nsec/nsec-badge/hw/2025/sao/Sao_Diamond/jlcpcb/production_files/BOM-Sao_Diamond.csv

Comment | Designator | Footprint | LCSC | Quantity
LED | D2 | LED_D3.0mm |  | 1
LED | D1 | LED_D3.0mm |  | 1
330 | R1 | R_Axial_DIN0204_L3.6mm_D1.6mm_P7.62mm_Horizontal |  | 1
330 | R2 | R_Axial_DIN0204_L3.6mm_D1.6mm_P7.62mm_Horizontal |  | 1
SAO Connector SMD | J1 | SAO Connector SMD |  | 1
