nsec/nsec-badge/hw/2025/sao/Sao_SlotMachine_v2/jlcpcb/production_files/BOM-Sao_SlotMachine_v2.csv

Comment | Designator | Footprint | LCSC | Quantity
330 | R3 | R_0805_2012Metric_Pad1.20x1.40mm_HandSolder |  | 1
330 | R1 | R_0805_2012Metric_Pad1.20x1.40mm_HandSolder |  | 1
330 | R2 | R_0805_2012Metric_Pad1.20x1.40mm_HandSolder |  | 1
SAO Connector SMD | J1 | SAO Connector SMD |  | 1
LED | D2 | LED_1206_3216Metric_Pad1.42x1.75mm_HandSolder |  | 1
LED | D3 | LED_1206_3216Metric_Pad1.42x1.75mm_HandSolder |  | 1
LED | D1 | LED_1206_3216Metric_Pad1.42x1.75mm_HandSolder |  | 1
