nsec/nsec-badge/hw/2023/confBadge/gerber/2022-11-17_confBadgeV1b/CAMOutputs/Assembly/BOM_JLCSMT.xlsx

Comment | Designator | Footprint | JLCPCB Part #（optional）
0.1uF | C1 C2 C3 C4 C5 C6 C7 C8 C9 C10 C11 C12 C13 C14 C15 C16 C17 C18 C19 C20 | 0603-CAP | C14663
100K | R7 | 0603-NO | C25803
10118192-0002LF | J1 | AMPHENOL_10118192-0002LF | C132564
10K | R2 | 0603-RES | C25804
10uF | C27 | 0805-NO | C440198
1K | R13 R14 | 0603-NO | C21190
1uF | C21 C26 | 0603-NO | C15849
330r | R6 | 0603-RES | C23138
8/16/20MHz | Q1 | RESONATOR-SMD-1:1 | C32180
AP2112-3.3 | U2 | SOT23-5 | C150742
ATMEGA328 | U1 | TQFP32-08 | C14877
CH340C | U7 | SOIC127P600X180-16N | C84681
BTN | S2 S3 S5 S6 S7 S4 | TACTILE_SWITCH_SMD_5.2MM | C318884
MBR120 | D3 D4 | SOD-123 | C130880
RED | D1 D2 D5 | CHIPLED_0805_NOOUTLINE | C84256
SMF05CT1G | U8 | SOT65P210X110-6N | C558443
WS2812-2020 | U3 U4 U9 U10 U11 U12 U13 U14 U15 U16 U17 U18 U19 U20 U21 U22 | LED_WS2812-2020 | C965555
