nsec/nsec-badge/esp32/components/cmd/cmd.c

/* Console example

   This example code is in the Public Domain (or CC0 licensed, at your option.)

   Unless required by applicable law or agreed to in writing, this
   software is distributed on an "AS IS" BASIS, WITHOUT WARRANTIES OR
   CONDITIONS OF ANY KIND, either express or implied.
*/

#include "argtable3/argtable3.h"
#include "cmd_decl.h"
#include "driver/uart.h"
#include "esp_console.h"
#include "esp_log.h"
#include "esp_system.h"
#include "esp_vfs_dev.h"
#include "esp_vfs_fat.h"
#include "linenoise/linenoise.h"
#include "nvs.h"
#include "nvs_flash.h"
#include <stdio.h>
#include <string.h>

#include "cmd.h"

static const char *TAG = "console";

static struct {
    const char *n_line, *sec_line;
} nsec_rows[] = {
    // clang-format off
    {"                       ", "                                        `/ydmmmdy+.      "},
    {"                       ", "                                       /mNNmhyhmNNNy`    "},
    {"                       ", "                                      :NNN+`    -dNNh    "},
    {"     -ohy  `:+oo+/.    ", "  -+yhdmmdhyo/.      .:/+++/:.        /NNd-:/+++/oNNN`   "},
    {"  :hNMMMh-hMMMMMMMMNo  ", ":dNNNNNNNNNNNNNd. -sdNNNNNNNNNds-     /NNNNNNNNNNNNNm-   "},
    {"  sMMMMMNMMMMMMMMMMMMd ", "hNNNNmyssydNNNm/.yNNNNNNNNNNNNNNNy` `sNNNNNNNNNNNNNNNm/  "},
    {"  sMMMMMMMy+/+yNMMMMMM+", " NNNN/     `:o:-mNNNNmo-` `-sNNNNNd:mNNNNNdo:--:+yNms`   "},
    {"  sMMMMMN.     .NMMMMMy", " mNNNNho/-`   `mNNNNm-       /NNNNNNNNNNNo        ..     "},
    {"  sMMMMMh       hMMMMMy", " mNNNNNNNNNds/+NNNNNdsssssssssNNNNNNNNNNh                "},
    {"  sMMMMMh       hMMMMMy", " -odNNNNNNNNNNNNNNNNNNNNNNNNNNNNNNNNNNNNy                "},
    {"  sMMMMMh       hMMMMMy", "    `-/oydNNNNNNNNNNm:::::::::::::/NNNNNm.               "},
    {"  sMMMMMh       hMMMMMy", " o:`      .mNNNNNNNNNy.       -o-  sNNNNNm+`     .oy:    "},
    {"  sMMMMMh       hMMMMMy", " mNmhs+//+yNNNNNdNNNNNNhsoosymNNNh: omNNNNNNdhyhmNNNNh:  "},
    {"  sMMMMMh       hMMMMMy", " mNNNNNNNNNNNNNy`-ymNNNNNNNNNNNNmy-  .smNNNNNNNNNNNNms.  "},
    {"  +hhhhho       ohhhhho", " /shmNNNNNNmho-    `:oyhdmmmdyo:`      `:oyhdmmddyo:`    "},
    {"                       ", "      `..``                                              "},
    // clang-format on
};

void initialize_nvs(void)
{
    esp_err_t err = nvs_flash_init();
    if (err == ESP_ERR_NVS_NO_FREE_PAGES ||
        err == ESP_ERR_NVS_NEW_VERSION_FOUND) {
        ESP_ERROR_CHECK(nvs_flash_erase());
        err = nvs_flash_init();
    }
    ESP_ERROR_CHECK(err);
}

static void initialize_console(void)
{
    /* Drain stdout before reconfiguring it */
    fflush(stdout);
    fsync(fileno(stdout));

    /* Disable buffering on stdin */
    setvbuf(stdin, NULL, _IONBF, 0);

    /* Minicom, screen, idf_monitor send CR when ENTER key is pressed */
    esp_vfs_dev_uart_set_rx_line_endings(ESP_LINE_ENDINGS_CR);
    /* Move the caret to the beginning of the next line on '\n' */
    esp_vfs_dev_uart_set_tx_line_endings(ESP_LINE_ENDINGS_CRLF);

    /* Configure UART. Note that REF_TICK is used so that the baud rate remains
     * correct while APB frequency is changing in light sleep mode.
     */
    const uart_config_t uart_config = {
        .baud_rate = CONFIG_ESP_CONSOLE_UART_BAUDRATE,
        .data_bits = UART_DATA_8_BITS,
        .parity = UART_PARITY_DISABLE,
        .stop_bits = UART_STOP_BITS_1,
        .source_clk = UART_SCLK_REF_TICK,
    };
    /* Install UART driver for interrupt-driven reads and writes */
    ESP_ERROR_CHECK(
        uart_driver_install(CONFIG_ESP_CONSOLE_UART_NUM, 256, 0, 0, NULL, 0));
    ESP_ERROR_CHECK(
        uart_param_config(CONFIG_ESP_CONSOLE_UART_NUM, &uart_config));

    /* Tell VFS to use UART driver */
    esp_vfs_dev_uart_use_driver(CONFIG_ESP_CONSOLE_UART_NUM);

    /* Initialize the console */
    esp_console_config_t console_config = {
        .max_cmdline_args = 8,
        .max_cmdline_length = 256,
#if CONFIG_LOG_COLORS
        .hint_color = atoi(LOG_COLOR_CYAN)
#endif
    };
    ESP_ERROR_CHECK(esp_console_init(&console_config));

    /* Configure linenoise line completion library */
    /* Enable multiline editing. If not set, long commands will scroll within
     * single line.
     */
    linenoiseSetMultiLine(1);

    /* Tell linenoise where to get command completions and hints */
    linenoiseSetCompletionCallback(&esp_console_get_completion);
    linenoiseSetHintsCallback((linenoiseHintsCallback *)&esp_console_get_hint);

    /* Set command history size */
    linenoiseHistorySetMaxLen(100);
}

void console_task(void *parm)
{

    initialize_console();

    /* Diplay Nsec banner */
    fputc('\n', stdout);
    for (int i = 0; i < sizeof(nsec_rows) / sizeof(nsec_rows[0]); i++) {
        fwrite(nsec_rows[i].n_line, 1, strlen(nsec_rows[i].n_line), stdout);
        fwrite(nsec_rows[i].sec_line, 1, strlen(nsec_rows[i].sec_line), stdout);
        fputc('\n', stdout);
    }

    /* Register commands */
    esp_console_register_help_command();
    register_system();
    register_wifi();
    register_neopixel();

    // register_nvs();

    /* Prompt to be printed before each line.
     * This can be customized, made dynamic, etc.
     */
    const char *prompt = LOG_COLOR_I "nsec-badge> " LOG_RESET_COLOR;

    printf("\n"
           "Welcome to the nsec badge console!\n"
           "Type 'help' to get the list of commands.\n"
           "Use UP/DOWN arrows to navigate through command history.\n"
           "Press TAB when typing command name to auto-complete.\n");

    /* Figure out if the terminal supports escape sequences */
    int probe_status = linenoiseProbe();
    if (probe_status) { /* zero indicates success */
        printf("\n"
               "Your terminal application does not support escape sequences.\n"
               "Line editing and history features are disabled.\n"
               "On Windows, try using Putty instead.\n");
        linenoiseSetDumbMode(1);
#if CONFIG_LOG_COLORS
        /* Since the terminal doesn't support escape sequences,
         * don't use color codes in the prompt.
         */
        prompt = "nsec-badge> ";
#endif // CONFIG_LOG_COLORS
    }

    /* Main loop */
    while (true) {
        /* Get a line using linenoise.
         * The line is returned when ENTER is pressed.
         */
        char *line = linenoise(prompt);
        if (line == NULL) { /* Ignore empty lines */
            continue;
        }
        /* Add the command to the history */
        linenoiseHistoryAdd(line);

        /* Try to run the command */
        int ret;
        esp_err_t err = esp_console_run(line, &ret);
        if (err == ESP_ERR_NOT_FOUND) {
            printf("Unrecognized command\n");
        } else if (err == ESP_ERR_INVALID_ARG) {
            // command was empty
        } else if (err == ESP_OK && ret != ESP_OK) {
            printf("Command returned non-zero error code: 0x%x (%s)\n", ret,
                   esp_err_to_name(ret));
        } else if (err != ESP_OK) {
            printf("Internal error: %s\n", esp_err_to_name(err));
        }
        /* linenoise allocates line buffer on the heap, so need to free it */
        linenoiseFree(line);
    }
}
