nsec/nsec-badge/nrf52/nsec_led_settings.c

/*
 * Copyright 2018 Eric Tremblay <habscup@gmail.com>
 *
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
 * THE SOFTWARE IS PROVIDED "AS IS", WITHOUT WARRANTY OF ANY KIND, EXPRESS OR
 * IMPLIED, INCLUDING BUT NOT LIMITED TO THE WARRANTIES OF MERCHANTABILITY,
 * FITNESS FOR A PARTICULAR PURPOSE AND NONINFRINGEMENT. IN NO EVENT SHALL THE
 * AUTHORS OR COPYRIGHT HOLDERS BE LIABLE FOR ANY CLAIM, DAMAGES OR OTHER
 * LIABILITY, WHETHER IN AN ACTION OF CONTRACT, TORT OR OTHERWISE, ARISING FROM,
 * OUT OF OR IN CONNECTION WITH THE SOFTWARE OR THE USE OR OTHER DEALINGS IN THE
 * SOFTWARE.
 */

#include <nrf.h>
#include <nordic_common.h>
#include <stdio.h>
#include <stdbool.h>
#include "ble/nsec_ble.h"
#include "status_bar.h"
#include "app_glue.h"
#include "controls.h"
#include "nsec_led_settings.h"
#include "nsec_settings.h"
#include "menu.h"
#include "gfx_effect.h"
#include "ssd1306.h"
#include "ws2812fx.h"
#include "nsec_storage.h"

#define BRIGHNESS_MENU_INDEX        0

#define SUPER_LOW_BRIGHTNESS_INDEX  0
#define LOW_BRIGHTNESS_INDEX        1
#define MEDIUM_BRIGHTNESS_INDEX     2
#define HIGH_BRIGHTNESS_INDEX       3
#define MAX_BRIGHTNESS_INDEX        4

#define SUPER_SLOW_SPEED_INDEX      0
#define SLOW_SPEED_INDEX            1
#define MEDIUM_SPEED_INDEX          2
#define FAST_SPEED_INDEX            3
#define SUPER_FAST_SPEED_INDEX      4

#define RED_INDEX                   0
#define GREEN_INDEX                 1
#define BLUE_INDEX                  2
#define WHITE_INDEX                 3
#define BLACK_INDEX                 4
#define YELLOW_INDEX                5
#define CYAN_INDEX                  6
#define MAGENTA_INDEX               7
#define PURPLE_INDEX                8
#define ORANGE_INDEX                9

enum setting_state {
    SETTING_STATE_CLOSED,
    SETTING_STATE_MENU,
    SETTING_STATE_BRIGHTNESS,
    SETTING_STATE_SPEED,
    SETTING_STATE_FIRST_COLOR,
    SETTING_STATE_SECOND_COLOR,
    SETTING_STATE_THIRD_COLOR,
    SETTING_STATE_REVERSE,
    SETTING_STATE_CONTROL,
};

static enum setting_state _state = SETTING_STATE_CLOSED;

static void show_brightness_menu(uint8_t item);
static void show_speed_menu(uint8_t item);
static void show_color_menu(uint8_t item);
static void save_brightness(uint8_t item);
static void save_speed(uint8_t item);
static void save_color(uint8_t item);
static void save_reverse(uint8_t item);
static void save_control(uint8_t item); 
static void show_reverse_menu(uint8_t item);
static void show_control_menu(uint8_t item);
static void set_led_default(uint8_t item);

static void setting_handle_buttons(button_t button);

static menu_item_s settings_items[] = {
    {
        .label = "Led brightness",
        .handler = show_brightness_menu,
    }, {
        .label = "Led speed",
        .handler = show_speed_menu,
    }, {
        .label = "Led first color",
        .handler = show_color_menu,
    },  {
        .label = "Led second color",
        .handler = show_color_menu,
    }, {
        .label = "Led third color",
        .handler = show_color_menu,
    }, {
        .label = "Reverse pattern",
        .handler = show_reverse_menu,
    }, {
        .label = "Turn led on/off",
        .handler = show_control_menu,
    }, {
        .label = "Factory default",
        .handler = set_led_default,
    }
};

static menu_item_s brightness_items[] = {
    {
        .label = "Super low",
        .handler = save_brightness,
    }, {
        .label = "Low",
        .handler = save_brightness,
    }, {
        .label = "Medium",
        .handler = save_brightness,
    }, {
        .label = "High",
        .handler = save_brightness,
    }, {
        .label = "Max",
        .handler = save_brightness,
    }
};

static menu_item_s speed_items[] = {
    {
        .label = "Super slow",
        .handler = save_speed,
    }, {
        .label = "Slow",
        .handler = save_speed,
    }, {
        .label = "Medium",
        .handler = save_speed,
    }, {
        .label = "Fast",
        .handler = save_speed,
    }, {
        .label = "Super fast",
        .handler = save_speed,
    }
};

static menu_item_s color_items[] = {
    {
        .label = "Red",
        .handler = save_color,
    }, {
        .label = "Green",
        .handler = save_color,
    }, {
        .label = "Blue",
        .handler = save_color,
    }, {
        .label = "White",
        .handler = save_color,
    }, {
        .label = "Black",
        .handler = save_color,
    }, {
        .label = "Yellow",
        .handler = save_color,
    }, {
        .label = "Cyan",
        .handler = save_color,
    }, {
        .label = "Magenta",
        .handler = save_color,
    }, {
        .label = "Purple",
        .handler = save_color,
    }, {
        .label = "Orange",
        .handler = save_color,
    } 
};

static menu_item_s reverse_items[] = {
    {
        .label = "False",
        .handler = save_reverse,
    }, {
        .label = "True",
        .handler = save_reverse,
    }
};

static menu_item_s control_items[] = {
    {
        .label = "OFF",
        .handler = save_control,
    }, {
        .label = "ON",
        .handler = save_control,
    }
};

void nsec_show_led_settings(void) {
    gfx_fill_rect(0, 8, 128, 65, SSD1306_BLACK);
    menu_init(0, 12, 128, 64 - 12, ARRAY_SIZE(settings_items), settings_items);
    nsec_controls_add_handler(setting_handle_buttons);
    _state = SETTING_STATE_MENU;
}

void show_actual_brightness(void) {
    uint8_t brightness = getBrightness_WS2812FX();
    char actual[50] = {0};
    if (brightness <= SUPER_LOW_BRIGHTNESS) {
        snprintf(actual, 50, "Now: %s", "Super Low");
    } else  if (brightness <= LOW_BRIGHTNESS) {
        snprintf(actual, 50, "Now: %s", "Low");
    } else if (brightness <= MEDIUM_BRIGHTNESS) {
        snprintf(actual, 50, "Now: %s", "Medium");
    } else if (brightness <= HIGH_BRIGHTNESS) {
        snprintf(actual, 50, "Now: %s", "High");
    } else {
        snprintf(actual, 50, "Now: %s", "Max");
    }

    gfx_fill_rect(12, 20, 128, 65, SSD1306_BLACK);
    gfx_set_cursor(0, 12);
    gfx_set_text_background_color(SSD1306_WHITE, SSD1306_BLACK);
    gfx_puts(actual);
}

static void show_brightness_menu(uint8_t item) {
    menu_close();
    gfx_fill_rect(0, 8, 128, 65, SSD1306_BLACK);
    show_actual_brightness();
    menu_init(0, 24, 128, 64 - 24, ARRAY_SIZE(brightness_items), brightness_items);
    _state = SETTING_STATE_BRIGHTNESS;
}

static void save_brightness(uint8_t item) {
    menu_take_over();
    switch(item) {
        case SUPER_LOW_BRIGHTNESS_INDEX:
            setBrightness_WS2812FX(SUPER_LOW_BRIGHTNESS);
            break;
        case LOW_BRIGHTNESS_INDEX:
            setBrightness_WS2812FX(LOW_BRIGHTNESS);
            break;
        case MEDIUM_BRIGHTNESS_INDEX:
            setBrightness_WS2812FX(MEDIUM_BRIGHTNESS);
            break;
        case HIGH_BRIGHTNESS_INDEX:
            setBrightness_WS2812FX(HIGH_BRIGHTNESS);
            break;
        case MAX_BRIGHTNESS_INDEX:
            setBrightness_WS2812FX(MAX_BRIGHTNESS);
            break;
        default:
            break;
    }

    update_stored_brightness(getBrightness_WS2812FX());
    show_brightness_menu(0);
}

void show_actual_speed(void) {
    uint16_t speed = getSpeed_WS2812FX();
    char actual[50] = {0};
    if (speed >= SUPER_SLOW_SPEED) {
        snprintf(actual, 50, "Now: %s", "Super slow");
    } else  if (speed >= SLOW_SPEED) {
        snprintf(actual, 50, "Now: %s", "Slow");
    } else if (speed >= MEDIUM_SPEED) {
        snprintf(actual, 50, "Now: %s", "Medium");
    } else if (speed >= FAST_SPEED) {
        snprintf(actual, 50, "Now: %s", "Fast");
    } else {
        snprintf(actual, 50, "Now: %s", "Super fast");
    }

    gfx_fill_rect(12, 20, 128, 65, SSD1306_BLACK);
    gfx_set_cursor(0, 12);
    gfx_set_text_background_color(SSD1306_WHITE, SSD1306_BLACK);
    gfx_puts(actual);
}

static void show_speed_menu(uint8_t item) {
    menu_close();
    gfx_fill_rect(0, 8, 128, 65, SSD1306_BLACK);
    show_actual_speed();
    menu_init(0, 24, 128, 64 - 24, ARRAY_SIZE(speed_items), speed_items);
    _state = SETTING_STATE_SPEED;
}

static void save_speed(uint8_t item) {
    menu_take_over();
    switch(item) {
        case SUPER_SLOW_SPEED_INDEX:
            setSpeed_WS2812FX(SUPER_SLOW_SPEED);
            break;
        case SLOW_SPEED_INDEX:
            setSpeed_WS2812FX(SLOW_SPEED);
            break;
        case MEDIUM_SPEED_INDEX:
            setSpeed_WS2812FX(MEDIUM_SPEED);
            break;
        case FAST_SPEED_INDEX:
            setSpeed_WS2812FX(FAST_SPEED);
            break;
        case SUPER_FAST_SPEED_INDEX:
            setSpeed_WS2812FX(SUPER_FAST_SPEED);
            break;
        default:
            break;
    }

    update_stored_speed(getSpeed_WS2812FX());
    show_speed_menu(0);
}

void show_actual_color(void) {
    uint32_t color;
    if (_state == SETTING_STATE_FIRST_COLOR) {
        color = getArrayColor_WS2812FX(0);
    } else if (_state == SETTING_STATE_SECOND_COLOR) {
        color = getArrayColor_WS2812FX(1);
    } else {
        color = getArrayColor_WS2812FX(2);
    }
    
    char actual[50] = {0};
    if (color == RED) {
        snprintf(actual, 50, "Now: %s", "Red");
    } else  if (color == GREEN) {
        snprintf(actual, 50, "Now: %s", "Green");
    } else if (color == BLUE) {
        snprintf(actual, 50, "Now: %s", "Blue");
    } else if (color == WHITE) {
        snprintf(actual, 50, "Now: %s", "White");
    } else if (color == BLACK) {
        snprintf(actual, 50, "Now: %s", "Black");
    } else if (color == YELLOW) {
        snprintf(actual, 50, "Now: %s", "Yellow");
    } else if (color == CYAN) {
        snprintf(actual, 50, "Now: %s", "Cyan");
    } else if (color == PURPLE) {
        snprintf(actual, 50, "Now: %s", "Purple");
    } else {
        snprintf(actual, 50, "Now: %s", "Orange");
    }

    gfx_fill_rect(12, 20, 128, 65, SSD1306_BLACK);
    gfx_set_cursor(0, 12);
    gfx_set_text_background_color(SSD1306_WHITE, SSD1306_BLACK);
    gfx_puts(actual);
}

static void show_color_menu(uint8_t item) {
    if (item == 2) {
        _state = SETTING_STATE_FIRST_COLOR;
    } else if (item == 3) {
        _state = SETTING_STATE_SECOND_COLOR;
    } else {
        _state = SETTING_STATE_THIRD_COLOR;
    }
    menu_close();
    gfx_fill_rect(0, 8, 128, 65, SSD1306_BLACK);
    show_actual_color();
    menu_init(0, 24, 128, 64 - 24, ARRAY_SIZE(color_items), color_items);
}

void set_color(uint32_t color) {
    if (_state == SETTING_STATE_FIRST_COLOR) {
        setArrayColor_packed_WS2812FX(color, 0);
        update_stored_color(color, 0);
    } else if (_state == SETTING_STATE_SECOND_COLOR) {
        setArrayColor_packed_WS2812FX(color, 1);
        update_stored_color(color, 1);
    } else {
        setArrayColor_packed_WS2812FX(color, 2);
        update_stored_color(color, 2);
    }
}

static void save_color(uint8_t item) {
    menu_take_over();
    switch(item) {
        case RED_INDEX:
            set_color(RED);
            break;
        case GREEN_INDEX:
            set_color(GREEN);
            break;
        case BLUE_INDEX:
            set_color(BLUE);
            break;
        case WHITE_INDEX:
            set_color(WHITE);
            break;
        case BLACK_INDEX:
            set_color(BLACK);
            break;
        case YELLOW_INDEX:
            set_color(YELLOW);
            break;
        case CYAN_INDEX:
            set_color(CYAN);
            break;
        case MAGENTA_INDEX:
            set_color(MAGENTA);
            break;
        case PURPLE_INDEX:
            set_color(PURPLE);
            break;
        case ORANGE_INDEX:
            set_color(ORANGE);
            break;
        default:
            break;
    }

    menu_take_over();
    show_color_menu(0);
}

void show_actual_reverse(void) {
    bool reverse = getReverse_WS2812FX();
    char actual[10] = {0};
    if (reverse) {
        snprintf(actual, 50, "Now: %s", "True");
    } else {
        snprintf(actual, 50, "Now: %s", "False");
    }

    gfx_fill_rect(12, 20, 128, 65, SSD1306_BLACK);
    gfx_set_cursor(0, 12);
    gfx_set_text_background_color(SSD1306_WHITE, SSD1306_BLACK);
    gfx_puts(actual);
}

static void show_reverse_menu(uint8_t item) {
    menu_close();
    gfx_fill_rect(0, 8, 128, 65, SSD1306_BLACK);
    show_actual_reverse();
    menu_init(0, 24, 128, 64 - 24, ARRAY_SIZE(reverse_items), reverse_items);
    _state = SETTING_STATE_REVERSE;
}

static void save_reverse(uint8_t item) {
    menu_take_over();
    setReverse_WS2812FX((bool)item);
    update_stored_reverse((bool)item);
    show_reverse_menu(0);
}

void show_actual_control(void) {
    bool control = isRunning_WS2812FX();
    char actual[10] = {0};
    if (control) {
        snprintf(actual, 50, "Now: %s", "ON");
    } else {
        snprintf(actual, 50, "Now: %s", "OFF");
    }

    gfx_fill_rect(12, 20, 128, 65, SSD1306_BLACK);
    gfx_set_cursor(0, 12);
    gfx_set_text_background_color(SSD1306_WHITE, SSD1306_BLACK);
    gfx_puts(actual);
}

static void show_control_menu(uint8_t item) {
    menu_close();
    gfx_fill_rect(0, 8, 128, 65, SSD1306_BLACK);
    show_actual_control();
    menu_init(0, 24, 128, 64 - 24, ARRAY_SIZE(control_items), control_items);
    _state = SETTING_STATE_CONTROL;
}

static void save_control(uint8_t item) {
    if (item) {
        start_WS2812FX();
    } else {
        stop_WS2812FX();
    }
    update_stored_control((bool)item);
    show_control_menu(0);
}

static void set_led_default(uint8_t item) {
    load_stored_led_default_settings();
}

static void setting_handle_buttons(button_t button) {
    if (button == BUTTON_BACK) {
        switch (_state) {
            case SETTING_STATE_MENU:
                _state = SETTING_STATE_CLOSED;
                menu_close();
                nsec_setting_show();
                break;

            case SETTING_STATE_BRIGHTNESS:
            case SETTING_STATE_SPEED:
            case SETTING_STATE_FIRST_COLOR:
            case SETTING_STATE_SECOND_COLOR:
            case SETTING_STATE_THIRD_COLOR:
            case SETTING_STATE_REVERSE:
            case SETTING_STATE_CONTROL:
                _state = SETTING_STATE_MENU;
                menu_close();
                nsec_show_led_settings();
                break;

            default:
                break;
        }
    }
}
