nsec/nsec-badge/nrf52/nsec_storage.c

/*
 * Copyright 2018 Eric Tremblay <habscup@gmail.com>
 *
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
 * THE SOFTWARE IS PROVIDED "AS IS", WITHOUT WARRANTY OF ANY KIND, EXPRESS OR
 * IMPLIED, INCLUDING BUT NOT LIMITED TO THE WARRANTIES OF MERCHANTABILITY,
 * FITNESS FOR A PARTICULAR PURPOSE AND NONINFRINGEMENT. IN NO EVENT SHALL THE
 * AUTHORS OR COPYRIGHT HOLDERS BE LIABLE FOR ANY CLAIM, DAMAGES OR OTHER
 * LIABILITY, WHETHER IN AN ACTION OF CONTRACT, TORT OR OTHERWISE, ARISING FROM,
 * OUT OF OR IN CONNECTION WITH THE SOFTWARE OR THE USE OR OTHER DEALINGS IN THE
 * SOFTWARE.
 */

#include <stdint.h>
#include <stdbool.h>
#include <string.h>

#include "nrf.h"
#include <nrf_delay.h>
#include "nordic_common.h"
#include "boards.h"

#include "nrf_sdh.h"
#include "nrf_sdh_ble.h"
#include "nrf_fstorage_sd.h"

#include "nsec_storage.h"
#include "led_code_storage.h"
#include "ws2812fx.h"
#include "nsec_led_settings.h"
#include "power.h"
#include "identity.h"
#include "display.h"
#include "gfx_effect.h"

#define PAGE_START_MAGIC    0xDEADC0DE

extern bool is_at_main_menu;

/* Led settings */
typedef struct LedSettings_t {
    uint8_t mode;
    uint16_t speed;
    uint8_t brightness;
    uint32_t colors[NUM_COLORS];
    bool reverse;
    bool control;
    bool is_ble_controlled;
    bool ble_control_permitted;
    SegmentBle segment_array[8];
} LedSettings;

LedSettings actual_settings;
LedSettings default_settings;
bool need_led_settings_update = false;

NRF_FSTORAGE_DEF(nrf_fstorage_t fs_led_settings) =
{
    .evt_handler = NULL,
    .start_addr = 0x68000,
    .end_addr   = 0x68FFF,
};

/* password */
uint32_t stored_password = 0;

NRF_FSTORAGE_DEF(nrf_fstorage_t fs_password) =
{
    .evt_handler = NULL,
    .start_addr = 0x69000,
    .end_addr   = 0x69FFF,
};
bool need_password_update = false;

/* identity */
char identity_name[17];

NRF_FSTORAGE_DEF(nrf_fstorage_t fs_identity) =
{
    .evt_handler = NULL,
    .start_addr = 0x70000,
    .end_addr   = 0x70FFF,
};

bool need_identity_update = false;

bool is_init = false;

static void wait_for_flash_ready(nrf_fstorage_t const * p_fstorage)
{
    /* While fstorage is busy*/
    while (nrf_fstorage_is_busy(p_fstorage)) {
        power_manage();
    }
}

void nsec_storage_update() {
    ret_code_t rc;

    if (need_led_settings_update) {
        rc = nrf_fstorage_erase(&fs_led_settings, fs_led_settings.start_addr, 1, NULL);
        APP_ERROR_CHECK(rc);
        wait_for_flash_ready(&fs_led_settings);

        rc = nrf_fstorage_write(&fs_led_settings, fs_led_settings.start_addr, &actual_settings,
                                sizeof(actual_settings), NULL);
        APP_ERROR_CHECK(rc);
        wait_for_flash_ready(&fs_led_settings);
        need_led_settings_update = false;
    }

    if (need_password_update) {
        rc = nrf_fstorage_erase(&fs_password, fs_password.start_addr, 1, NULL);
        APP_ERROR_CHECK(rc);
        wait_for_flash_ready(&fs_password);

        rc = nrf_fstorage_write(&fs_password, fs_password.start_addr, &stored_password, 4, NULL);
        APP_ERROR_CHECK(rc);
        wait_for_flash_ready(&fs_password);
        need_password_update = false;
    }

    if (need_identity_update) {
        rc = nrf_fstorage_erase(&fs_identity, fs_identity.start_addr, 1, NULL);
        APP_ERROR_CHECK(rc);
        wait_for_flash_ready(&fs_identity);

        rc = nrf_fstorage_write(&fs_identity, fs_identity.start_addr, identity_name, 
                                16, NULL);
        APP_ERROR_CHECK(rc);
        wait_for_flash_ready(&fs_identity);

        if (is_at_main_menu) {
            nsec_identity_draw();
            gfx_update();
        }
        need_identity_update = false;
    }
}

/* Led Settings interface */
void update_stored_brightness(uint8_t brightness) {
    actual_settings.brightness = brightness;
    need_led_settings_update = true;
}

void update_stored_mode(uint8_t mode) {
    actual_settings.mode = mode;
    need_led_settings_update = true;
}

void update_stored_speed(uint16_t speed) {
    actual_settings.speed = speed;
    need_led_settings_update = true;
}

void update_stored_color(uint32_t color, uint8_t index) {
    if (index < NUM_COLORS) {
        actual_settings.colors[index] = color;
        need_led_settings_update = true;
    }
}

void update_stored_reverse(bool reverse) {
    actual_settings.reverse = reverse;
    need_led_settings_update = true;
}

void update_stored_control(bool control) {
    actual_settings.control = control;
    need_led_settings_update = true;
}

void update_stored_segment(SegmentBle *segment, int index) {
    if (actual_settings.ble_control_permitted) {
        if (actual_settings.is_ble_controlled) {
            actual_settings.segment_array[index].active = segment->active;
            actual_settings.segment_array[index].index = segment->index;
            actual_settings.segment_array[index].start = segment->start;
            actual_settings.segment_array[index].stop = segment->stop;
            actual_settings.segment_array[index].speed = segment->speed;
            actual_settings.segment_array[index].mode = segment->mode;
            actual_settings.segment_array[index].reverse = segment->reverse;
            actual_settings.segment_array[index].colors[0] = segment->colors[0];
            actual_settings.segment_array[index].colors[1] = segment->colors[1];
            actual_settings.segment_array[index].colors[2] = segment->colors[2];

            need_led_settings_update = true;
        }
    }
}

void update_is_ble_controlled(bool ble_controlled) {
    if (actual_settings.ble_control_permitted) {
        actual_settings.is_ble_controlled = ble_controlled;
        need_led_settings_update = true;
    }
}

void update_ble_control_permitted(bool permitted) {
    actual_settings.ble_control_permitted = permitted;
    need_led_settings_update = true;
}

void load_stored_led_settings(void) {
    if (!is_init) {
        nsec_storage_init();
    }

    if (actual_settings.control) {
        start_WS2812FX();
    } else {
        stop_WS2812FX();
    }

    resetSegments_WS2812FX();

    if (!actual_settings.is_ble_controlled) {
        set_ble_controlled(false);
        setBrightness_WS2812FX(actual_settings.brightness);
        setMode_WS2812FX(actual_settings.mode);
        setSpeed_WS2812FX(actual_settings.speed);
        setArrayColor_packed_WS2812FX(actual_settings.colors[0], 0);
        setArrayColor_packed_WS2812FX(actual_settings.colors[1], 1);
        setArrayColor_packed_WS2812FX(actual_settings.colors[2], 2);
        setReverse_WS2812FX(actual_settings.reverse);
    } else {
        set_ble_controlled(true);
        for (int i = 0; i < ARRAY_SIZE(actual_settings.segment_array); i++) {
            if (actual_settings.segment_array[i].active) {
                setSegment_color_array_WS2812FX(actual_settings.segment_array[i].index,
                actual_settings.segment_array[i].start,
                actual_settings.segment_array[i].stop,
                actual_settings.segment_array[i].mode, 
                actual_settings.segment_array[i].colors,
                actual_settings.segment_array[i].speed,
                actual_settings.segment_array[i].reverse);
            }
        }
        update_all_characteristics_value();
    }
}

void load_stored_led_default_settings(void) {
     memcpy(&actual_settings, &default_settings, sizeof(LedSettings));
     need_led_settings_update = true;
     load_stored_led_settings();
}

/* code interface */

static void unlock_all_pattern() {
    if (stored_password != 0x00FFFFFF) {
        stored_password = 0x00FFFFFF;
        need_password_update = true;
    }
}

static void unlock_pattern(uint32_t sponsor_index) {
    if (sponsor_index < 31) {
        SET_BIT(stored_password, sponsor_index);
        need_password_update = true;
    }
}

const char * nsec_get_pattern_pw(uint32_t sponsor_index) {
    if (sponsor_index < SPONSOR_PW_SIZE) {
        return sponsor_password[sponsor_index];
    }
    return 0;
}

bool pattern_is_unlock(uint32_t sponsor_index) {
    return IS_SET(stored_password, sponsor_index);
}

// true valid, false invalid
bool nsec_unlock_led_pattern(char *password, uint8_t index) {
    if (strcmp(password, MASTER_PW) == 0) {
        unlock_all_pattern();
        return true;
    }
    if (strcmp(password, sponsor_password[index]) == 0) {
        if (!pattern_is_unlock(index)) {
            unlock_pattern(index);
        }
        return true;
    }
    return false;
}

// identity
void update_identity(char *new_identity) {
    memset(identity_name, 0, 16);
    strncpy(identity_name, new_identity, 16);
    need_identity_update = true;
}

void load_stored_identity(char *identity) {
    if (!is_init) {
        nsec_storage_init();
    }
    memset(identity, 0, 16);
    strncpy(identity, identity_name, 16);
}

static bool is_new_memory_page(nrf_fstorage_t const * p_fstorage) {
    ret_code_t rc;
    uint32_t new_dev_memory;
    rc = nrf_fstorage_read(p_fstorage, p_fstorage->start_addr, &new_dev_memory, 4);
    APP_ERROR_CHECK(rc);
    wait_for_flash_ready(p_fstorage);

    return (new_dev_memory == 0xFFFFFFFF) ? true : false;
} 

static void led_settings_storage_init(void) {
    ret_code_t rc;

    nrf_fstorage_api_t *p_fs_api;
    p_fs_api = &nrf_fstorage_sd;

    rc = nrf_fstorage_init(&fs_led_settings, p_fs_api, NULL);
    APP_ERROR_CHECK(rc);

    default_settings.mode = FX_MODE_STATIC;
    default_settings.speed = MEDIUM_SPEED;
    default_settings.brightness = MEDIUM_BRIGHTNESS;
    default_settings.colors[0] = BLUE;
    default_settings.colors[1] = RED;
    default_settings.colors[2] = GREEN;
    default_settings.reverse = false;
    default_settings.control = true;
    default_settings.is_ble_controlled = false;
    default_settings.ble_control_permitted = true;

    for (int i = 0; i < ARRAY_SIZE(default_settings.segment_array); i++) {
        default_settings.segment_array[i].active = false;
        default_settings.segment_array[i].index = 0;
        default_settings.segment_array[i].start = 0;
        default_settings.segment_array[i].stop = 0;
        default_settings.segment_array[i].speed = 1000;
        default_settings.segment_array[i].mode = 0;
        default_settings.segment_array[i].reverse = false;
        default_settings.segment_array[i].colors[0] = BLUE;
        default_settings.segment_array[i].colors[1] = RED;
        default_settings.segment_array[i].colors[2] = GREEN;
    }
    
    if (is_new_memory_page(&fs_led_settings)) {
        //Store the default settings
        rc = nrf_fstorage_write(&fs_led_settings, fs_led_settings.start_addr, &default_settings, 
                                sizeof(actual_settings), NULL);
        APP_ERROR_CHECK(rc);
        wait_for_flash_ready(&fs_led_settings);
    }

    //Load actual settings
    rc = nrf_fstorage_read(&fs_led_settings, fs_led_settings.start_addr, &actual_settings,
                            sizeof(actual_settings));
    APP_ERROR_CHECK(rc);
    wait_for_flash_ready(&fs_led_settings);
}

static void password_storage_init(void) {
    ret_code_t rc;

    nrf_fstorage_api_t *p_fs_api;
    p_fs_api = &nrf_fstorage_sd;

    rc = nrf_fstorage_init(&fs_password, p_fs_api, NULL);
    APP_ERROR_CHECK(rc);
    
    if (is_new_memory_page(&fs_password)) {
        //Store the default settings
        rc = nrf_fstorage_write(&fs_password, fs_password.start_addr, &stored_password, 4, NULL);
        APP_ERROR_CHECK(rc);
        wait_for_flash_ready(&fs_password);
    }

    //Load actual settings
    rc = nrf_fstorage_read(&fs_password, fs_password.start_addr, &stored_password, 4);
    APP_ERROR_CHECK(rc);
    wait_for_flash_ready(&fs_password);
}

static void identity_storage_init(void) {
    ret_code_t rc;

    nrf_fstorage_api_t *p_fs_api;
    p_fs_api = &nrf_fstorage_sd;

    rc = nrf_fstorage_init(&fs_identity, p_fs_api, NULL);
    APP_ERROR_CHECK(rc);
    
    if (is_new_memory_page(&fs_identity)) {
        //Store the default settings
#if defined(NSEC_HARDCODED_BADGE_IDENTITY_NAME)
            #define NSEC_STRINGIFY_(...) #__VA_ARGS__
            #define NSEC_STRINGIFY(...) NSEC_STRINGIFY_(__VA_ARGS__)
            snprintf(identity_name, 16, NSEC_STRINGIFY(NSEC_HARDCODED_BADGE_IDENTITY_NAME));
#else
            snprintf(identity_name, 16, "Cosmonaut #%02ld", (NRF_FICR->DEVICEID[0] & 0xFFFF));
#endif
        rc = nrf_fstorage_write(&fs_identity, fs_identity.start_addr, identity_name,
                                16, NULL);
        APP_ERROR_CHECK(rc);
        wait_for_flash_ready(&fs_identity);
    }

    //Load actual settings
    rc = nrf_fstorage_read(&fs_identity, fs_identity.start_addr, identity_name, 16);
    APP_ERROR_CHECK(rc);
    wait_for_flash_ready(&fs_identity);
}

void nsec_storage_init(void) {
   
    if (is_init) {
        return;
    }

    led_settings_storage_init();
    password_storage_init();
    identity_storage_init();

    is_init = true;
}
