nsec/nsec-badge/components/cmd_sys/cmd_sys.h

// SPDX-FileCopyrightText: 2025 NorthSec
//
// SPDX-License-Identifier: MIT

#pragma once

#ifdef __cplusplus
extern "C" {
#endif

// Register NVS functions
void console_register_cmd_sys(void);

#ifdef __cplusplus
}
#endif
