nsec/nsec-badge/nrf52/nsec_settings.c

//  Copyright (c) 2017
//  Benjamin Vanheuverzwijn <bvanheu@gmail.com>
//  Marc-Etienne M. Leveille <marc.etienne.ml@gmail.com>
//
//  License: MIT (see LICENSE for details)

#include <nrf.h>
#include <nordic_common.h>
#include <stdio.h>
#include "nsec_settings.h"
#include "nsec_led_settings.h"
#include "menu.h"
#include "display.h"
#include "gfx_effect.h"
#include "ble/nsec_ble.h"
#include "status_bar.h"
#include "app_glue.h"
#include "controls.h"
#include "identity.h"
#include "ws2812fx.h"
#include "nsec_storage.h"
#include "timer.h"

//static void toggle_bluetooth(uint8_t item);
static void show_credit(uint8_t item);
static void turn_off_screen(uint8_t item);
static void show_led_settings(uint8_t item);
static void toggle_flashlight(uint8_t item);
static void show_member_details(uint8_t item);
static void setting_handle_buttons(button_t button);

enum setting_state {
    SETTING_STATE_CLOSED,
    SETTING_STATE_MENU,
    SETTING_STATE_CREDIT,
    SETTING_STATE_CREDIT_DETAILS,
    SETTING_STATE_SCREEN_OFF,
    SETTING_STATE_FLASHLIGHT,
    SETTING_STATE_BATTERY,
};

static enum setting_state _state = SETTING_STATE_CLOSED;

static void setting_handle_buttons(button_t button);

static char sync_key_string[] = "Sync key: XXXX";

static menu_item_s settings_items[] = {
    {
        .label = "Led settings",
        .handler = show_led_settings,
    }, /*{
        .label = "Toggle Bluetooth",
        .handler = toggle_bluetooth,
    }, */{
        .label = "Turn screen off",
        .handler = turn_off_screen,
    }, {
        .label = "Flashlight",
        .handler = toggle_flashlight,
    }, {
        .label = "Credit",
        .handler = show_credit,
    }, {
        .label = sync_key_string,
        .handler = NULL,
    }
};

static menu_item_s members_items[] = {
    {
        .label = "Eric Tremblay",
        .handler = show_member_details,
    }, /*{
        .label = "Francois Charbonneau",
        .handler = show_member_details,
    }, */{
        .label = "Marc-Etienne Leveille",
        .handler = show_member_details,
    }, {
        .label = "Michael Jeanson",
        .handler = show_member_details,
    }, {
        .label = "Nicolas Aubry",
        .handler = show_member_details,
    }, {
        .label = "Thomas Dupuy",
        .handler = show_member_details,
    },
};

static void show_member_details(uint8_t item) {
    menu_close();
    gfx_fill_rect(0, 8, 128, 56, DISPLAY_BLACK);
    gfx_set_cursor(0, 8);
    gfx_set_text_background_color(DISPLAY_WHITE, DISPLAY_BLACK);
    _state = SETTING_STATE_CREDIT_DETAILS;

    switch (item) {
        //Line   |                     | 21 character
        // There is 7 lines under the status bar
        case 0: //Eric Tremblay
        gfx_puts("VP Badge nsec 2018\n");
        gfx_puts("etremblay.16@\n");
        gfx_puts("            gmail.com");
        gfx_puts("Hardware\n");
        gfx_puts("Software\n");
        break;

        case 1: // Marc-Etienne Leveille
        gfx_puts("Badge veteran nsec18\n");
        gfx_puts("Marc-Etienne Leveille\n");
        gfx_puts("marc-etienne@nsec.io\n");
        gfx_puts("@marc_etienne_\n");
        gfx_puts("shape//soft//new dad\n");
        break;

        case 2: //Michael Jeanson
        gfx_puts("Badge drone nsec 2018\n");
        gfx_puts("Michael Jeanson\n");
        gfx_puts("mjeanson@gmail.com\n");
        gfx_puts("@mjeanson\n");
        gfx_puts("Software\n");
        break;

        case 3: // Nicolas Aubry
        show_credit(4);
        break;

        case 4: //Thomas Dupuy
        show_credit(4);
        break;
    }
    gfx_update();
}

static void show_led_settings(uint8_t item) {
    menu_close();
    _state = SETTING_STATE_CLOSED;
    nsec_show_led_settings();
}

/*static void toggle_bluetooth(uint8_t item) {
    if(nsec_ble_toggle()) {
        nsec_status_set_ble_status(STATUS_BLUETOOTH_ON);
    }
    else {
        nsec_status_set_ble_status(STATUS_BLUETOOTH_OFF);
    }
}*/

static void show_credit(uint8_t item) {
    _state = SETTING_STATE_CREDIT;
    menu_close();
    gfx_fill_rect(0, 8, 128, 56, DISPLAY_BLACK);
    gfx_set_cursor(0, 8);
    gfx_set_text_background_color(DISPLAY_WHITE, DISPLAY_BLACK);
    gfx_puts("nsec 2018 badge team:");
    menu_init(0, 16, 128, 64 - 12, ARRAY_SIZE(members_items), members_items);
    gfx_update();
}

void show_battery_status(void) {
    _state = SETTING_STATE_BATTERY;
    menu_close();
    start_battery_status_timer();
    nsec_controls_add_handler(setting_handle_buttons);
}

static void toggle_flashlight(uint8_t item) {
    _state = SETTING_STATE_FLASHLIGHT;
    menu_close();
    gfx_fill_screen(DISPLAY_WHITE);
    gfx_update();
    setMode_WS2812FX(FX_MODE_STATIC);
    setBrightness_WS2812FX(255);
    setColor_packed_WS2812FX(WHITE);
}

static void turn_off_screen(uint8_t item) {
    menu_close();
    gfx_fill_screen(DISPLAY_BLACK);
    gfx_update();
    _state = SETTING_STATE_SCREEN_OFF;
}

void nsec_setting_show(void) {
    char key[8];
    nsec_identity_get_unlock_key(key, sizeof(key));
#ifdef NSEC_HIDE_SYNC_KEY_IN_SETTINGS
    snprintf(sync_key_string, sizeof(sync_key_string), "Sync key: %s", "XXXX");
#else
    snprintf(sync_key_string, sizeof(sync_key_string), "Sync key: %s", key);
#endif
    gfx_fill_rect(0, 8, 128, 65 - 8, DISPLAY_BLACK);
    menu_init(0, 12, 128, 64 - 12, ARRAY_SIZE(settings_items), settings_items);
    nsec_controls_add_handler(setting_handle_buttons);
    _state = SETTING_STATE_MENU;
}

static void setting_handle_buttons(button_t button) {
    if (button == BUTTON_BACK) {
        switch (_state) {
            case SETTING_STATE_MENU:
                _state = SETTING_STATE_CLOSED;
                menu_close();
                show_main_menu();
                break;

            case SETTING_STATE_CREDIT_DETAILS:
                show_credit(4);
                break;

            case SETTING_STATE_BATTERY:
                stop_battery_status_timer();
                // Battery status was moved to the main menu
                // this is a hack to make it work with minimal
                // code change
                _state = SETTING_STATE_CLOSED;
                menu_close();
                show_main_menu();
                break;

            case SETTING_STATE_FLASHLIGHT:
                load_stored_led_settings();
                // no break
            case SETTING_STATE_SCREEN_OFF:
                nsec_status_bar_ui_redraw();
                // no break
            case SETTING_STATE_CREDIT:
                nsec_setting_show();
                break;

            default:
                break;
        }
    }
}
