nsec/nsec-badge/components/ssd1306/badge_nsec_logo.cpp

/*
 * SPDX-License-Identifier: MIT
 *
 * Copyright 2025 Patrick Downing <padraignix@gmail.com>
 */

#include <stdio.h>
#include "badge_nsec_logo.h"
#include "badge_ssd1306_helper.hpp"

uint8_t logoNsecBitmap [] = {
0x00, 0x00, 0x00, 0x00, 0x00, 0x00, 0x00, 0x00, 0x00, 0x00, 0x00, 0x00, 0x00, 0x00, 0x00, 0x00, 
0x00, 0x00, 0x00, 0x00, 0x00, 0x00, 0x00, 0x00, 0x00, 0x00, 0x00, 0xf8, 0x00, 0x00, 0x00, 0x00, 
0x00, 0x00, 0x00, 0x00, 0x00, 0x00, 0x00, 0x00, 0x00, 0x00, 0x03, 0xfe, 0x00, 0x00, 0x00, 0x00, 
0x00, 0x00, 0x00, 0x00, 0x00, 0x00, 0x00, 0x00, 0x00, 0x00, 0x07, 0xff, 0x00, 0x00, 0x00, 0x00, 
0x00, 0x00, 0x00, 0x00, 0x00, 0x00, 0x00, 0x00, 0x00, 0x00, 0x0f, 0x8f, 0x80, 0x00, 0x00, 0x00, 
0x00, 0x00, 0x00, 0x00, 0x00, 0x00, 0x00, 0x00, 0x00, 0x00, 0x0f, 0x07, 0x80, 0x00, 0x00, 0x00, 
0x00, 0x00, 0x00, 0x00, 0x00, 0x00, 0x00, 0x00, 0x00, 0x00, 0x0e, 0x03, 0x80, 0x00, 0x00, 0x00, 
0x00, 0x00, 0x00, 0x00, 0x80, 0x00, 0x1f, 0xc0, 0x00, 0x00, 0x0e, 0x03, 0x80, 0x00, 0x00, 0x00, 
0x00, 0x00, 0x00, 0x03, 0x8f, 0xe0, 0x7f, 0xf8, 0x1f, 0xe0, 0x0f, 0xff, 0x80, 0x00, 0x00, 0x00, 
0x00, 0x00, 0x00, 0x0f, 0x9f, 0xf0, 0xff, 0xfe, 0x7f, 0xf8, 0x0f, 0xff, 0x80, 0x00, 0x00, 0x00, 
0x00, 0x00, 0x00, 0x1f, 0xff, 0xf9, 0xff, 0xfc, 0xff, 0xfc, 0x1f, 0xff, 0xc0, 0x00, 0x00, 0x00, 
0x00, 0x00, 0x00, 0x1f, 0xff, 0xfd, 0xff, 0xfd, 0xff, 0xfe, 0x3f, 0xff, 0xe0, 0x00, 0x00, 0x00, 
0x00, 0x00, 0x00, 0x1f, 0xff, 0xfd, 0xf0, 0x7b, 0xff, 0xff, 0x3f, 0xff, 0xc0, 0x00, 0x00, 0x00, 
0x00, 0x00, 0x00, 0x1f, 0xf3, 0xfc, 0xf0, 0x0b, 0xf0, 0x3f, 0x7f, 0x07, 0x80, 0x00, 0x00, 0x00, 
0x00, 0x00, 0x00, 0x1f, 0xc0, 0xfc, 0xf8, 0x07, 0xf0, 0x1f, 0xfe, 0x01, 0x00, 0x00, 0x00, 0x00, 
0x00, 0x00, 0x00, 0x1f, 0xc0, 0xfc, 0xfe, 0x07, 0xe0, 0x1f, 0xfc, 0x00, 0x00, 0x00, 0x00, 0x00, 
0x00, 0x00, 0x00, 0x1f, 0x80, 0xfc, 0xff, 0xc7, 0xe0, 0x1f, 0xfc, 0x00, 0x00, 0x00, 0x00, 0x00, 
0x00, 0x00, 0x00, 0x1f, 0x80, 0xfc, 0xff, 0xf7, 0xff, 0xff, 0xfc, 0x00, 0x00, 0x00, 0x00, 0x00, 
0x00, 0x00, 0x00, 0x1f, 0x80, 0xfc, 0xff, 0xff, 0xff, 0xff, 0xfc, 0x00, 0x00, 0x00, 0x00, 0x00, 
0x00, 0x00, 0x00, 0x1f, 0x80, 0xfc, 0x3f, 0xff, 0xff, 0xff, 0xfc, 0x00, 0x00, 0x00, 0x00, 0x00, 
0x00, 0x00, 0x00, 0x1f, 0x80, 0xfc, 0x0f, 0xff, 0xff, 0xff, 0xfc, 0x00, 0x00, 0x00, 0x00, 0x00, 
0x00, 0x00, 0x00, 0x1f, 0x80, 0xfc, 0x01, 0xff, 0xe0, 0x00, 0xfc, 0x00, 0x00, 0x00, 0x00, 0x00, 
0x00, 0x00, 0x00, 0x1f, 0x80, 0xfc, 0x00, 0x7f, 0xe0, 0x00, 0xfe, 0x01, 0x00, 0x00, 0x00, 0x00, 
0x00, 0x00, 0x00, 0x1f, 0x80, 0xfc, 0x80, 0x7f, 0xf0, 0x0c, 0x7f, 0x03, 0x80, 0x00, 0x00, 0x00, 
0x00, 0x00, 0x00, 0x1f, 0x80, 0xfc, 0xe0, 0x7f, 0xfc, 0x3e, 0x7f, 0xcf, 0xc0, 0x00, 0x00, 0x00, 
0x00, 0x00, 0x00, 0x1f, 0x80, 0xfc, 0xff, 0xff, 0xff, 0xff, 0x3f, 0xff, 0xe0, 0x00, 0x00, 0x00, 
0x00, 0x00, 0x00, 0x1f, 0x80, 0xfc, 0xff, 0xfc, 0xff, 0xff, 0x1f, 0xff, 0xe0, 0x00, 0x00, 0x00, 
0x00, 0x00, 0x00, 0x1f, 0x80, 0xfc, 0xff, 0xfc, 0x7f, 0xfc, 0x0f, 0xff, 0x80, 0x00, 0x00, 0x00, 
0x00, 0x00, 0x00, 0x1f, 0x80, 0xfc, 0xff, 0xf0, 0x3f, 0xf8, 0x03, 0xff, 0x00, 0x00, 0x00, 0x00, 
0x00, 0x00, 0x00, 0x00, 0x00, 0x00, 0x00, 0x00, 0x00, 0x00, 0x00, 0x00, 0x00, 0x00, 0x00, 0x00, 
0x00, 0x00, 0x00, 0x00, 0x00, 0x00, 0x00, 0x00, 0x00, 0x00, 0x00, 0x00, 0x00, 0x00, 0x00, 0x00, 
0x00, 0x00, 0x00, 0x00, 0x00, 0x00, 0x00, 0x00, 0x00, 0x00, 0x00, 0x00, 0x00, 0x00, 0x00, 0x00
};

extern "C" void badge_lcd_nsec_logo()
{
    badge_print_bitmap(logoNsecBitmap, 0, 0, 128, 32, false);
}
