nsec/nsec-badge/ctf-components/quantum/calibration.cpp

/*
 * SPDX-License-Identifier: MIT
 *
 * Copyright 2025 Patrick Downing <padraignix@gmail.com>
 */

#include "calibration.h"

#define QUANTUM_NAMESPACE "quantum"
static const char *TAG = "Calibration";

// Define the structure for calibration data
typedef struct {
    uint8_t calib[6];
    char hashes[6][6];
} CalibrationData;

// Using values for calibration data
CalibrationData calib_data = {
    {0, 0, 0, 0, 0, 0},
    {"00000", "00000", "00000", "00000", "00000", "00000"}
};

// Default values for calibration data
CalibrationData default_calib_data = {
    {0, 0, 0, 0, 0, 0},     // Default calibration values
    {"00000", "00000", "00000", "00000", "00000", "00000"}
};

bool leds_on = true;

void print_nvs_blob() {

    CalibrationData calib_data;
    size_t required_size = sizeof(CalibrationData);

    // Try to get the blob from NVS
    nvs_handle_t nvs_handle;
    esp_err_t err2 = nvs_open(QUANTUM_NAMESPACE, NVS_READONLY, &nvs_handle);
    if (err2 != ESP_OK) {
        ESP_LOGE(TAG, "CHECKING - Failed to open NVS namespace: %s\n", esp_err_to_name(err2));
        return;
    }
    err2 = nvs_get_blob(nvs_handle, "calib_data", &calib_data, &required_size);
    if (err2 == ESP_OK) {
        printf("CHECKING - NVS Calibration Data:\n");
        for (int i = 0; i < 6; i++) {
            printf("  calib[%d]: %d, hash[%d]: %s\n", i, calib_data.calib[i], i, calib_data.hashes[i]);
        }
    } else if (err2 == ESP_ERR_NVS_NOT_FOUND) {
        printf("No calibration data found in NVS.\n");
    } else {
        printf("Error reading NVS blob: %s\n", esp_err_to_name(err2));
    }
}
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
